XiaobaoAlex/NixieClock_WiFi_github/图片/aixin2.bmp

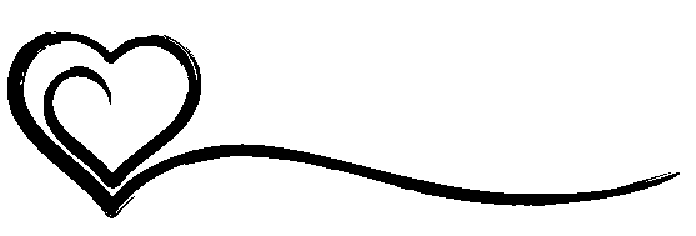
图片/aixin2.bmp
