XiaobaoAlex/NixieClock_WiFi_github/图片/duck.png

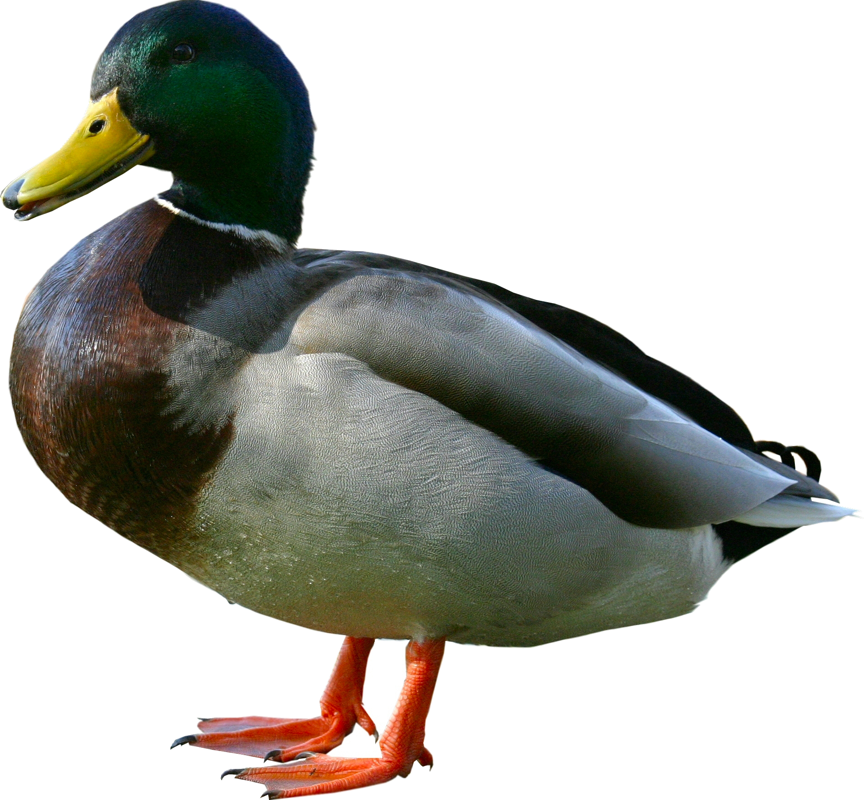
图片/duck.png
