XiaobaoAlex/NixieClock_WiFi_github/图片/lemon.png

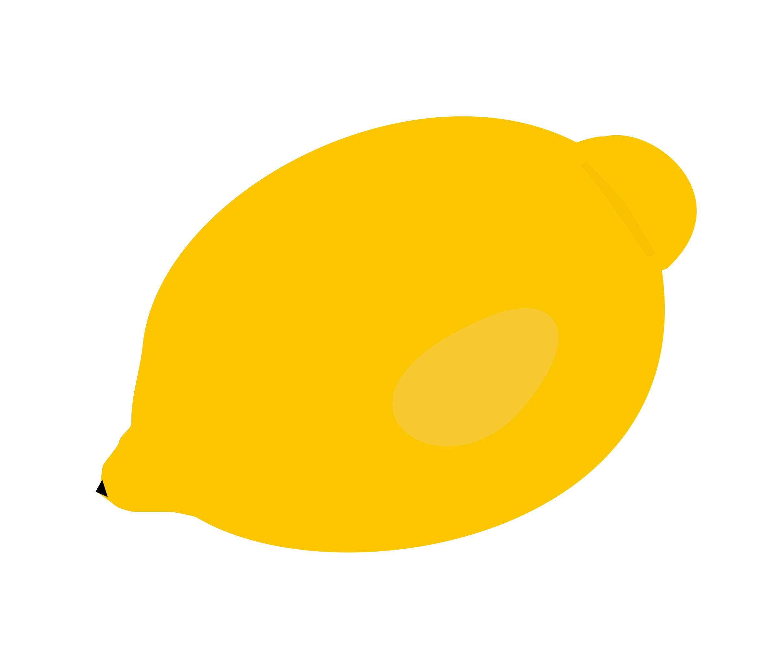
图片/lemon.png
