XiaobaoAlex/NixieClock_WiFi_github/图片/RigolDS0.png

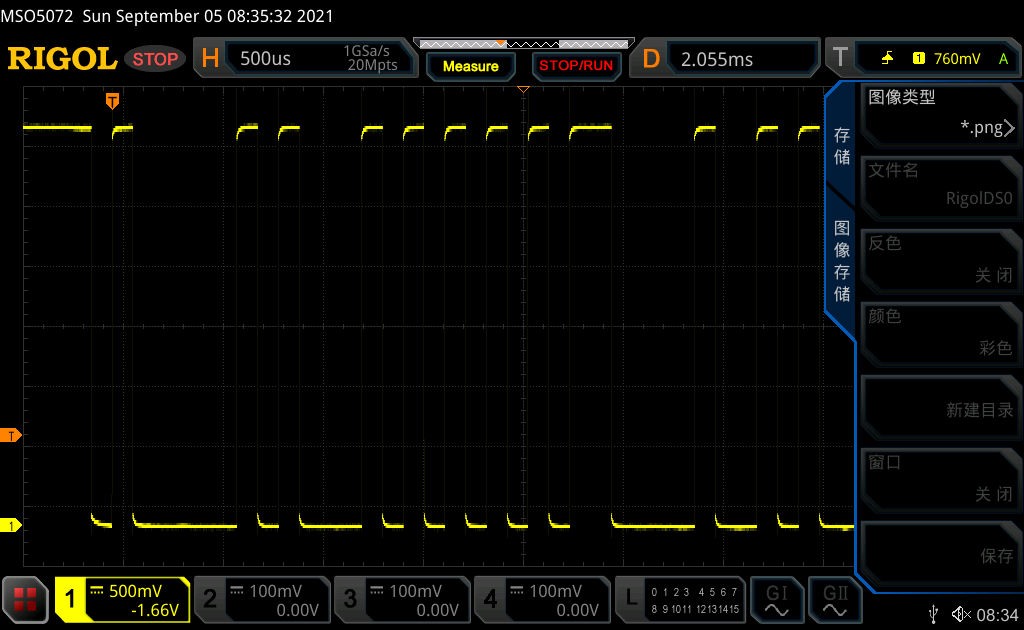
图片/RigolDS0.png
