XiaobaoAlex/NixieClock_WiFi_github/图片/shamrock_PNG82.png

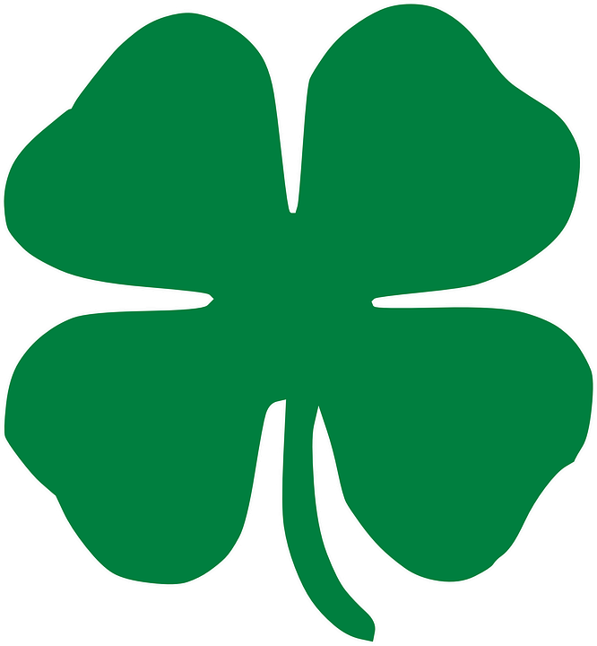
图片/shamrock_PNG82.png
