XiaobaoAlex/NixieClock_WiFi_github/图片/微信截图_20210717144708.png

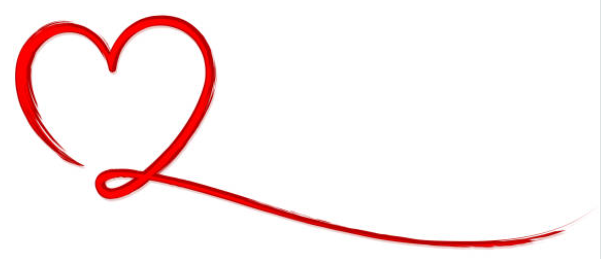
图片/微信截图_20210717144708.png
