XiaobaoAlex/NixieClock_WiFi_github/图片/爱心1.bmp

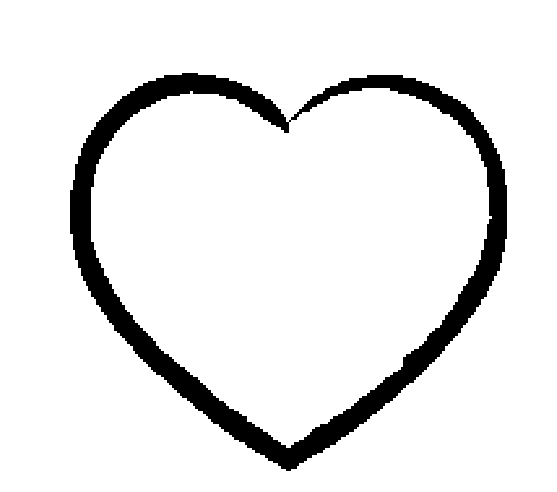
图片/爱心1.bmp
