XiaobaoAlex/NixieClock_WiFi_github/图片/黑色花边.bmp

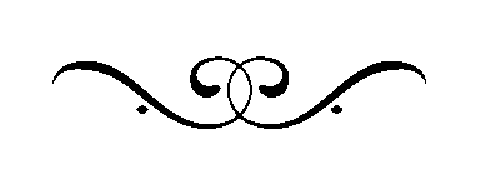
图片/黑色花边.bmp
