XiaobaoAlex/NixieClock_WiFi_github/数据手册/辉光管图纸.jpg

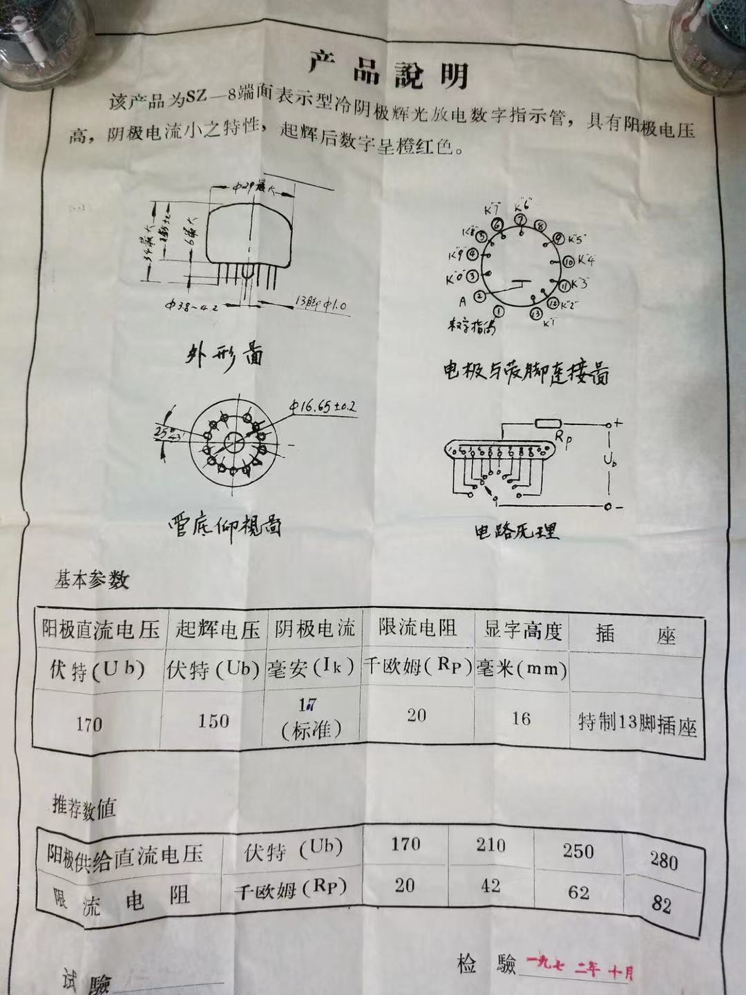
数据手册/辉光管图纸.jpg
